skot/bitaxe/doc/bitaxe_v2.jpg

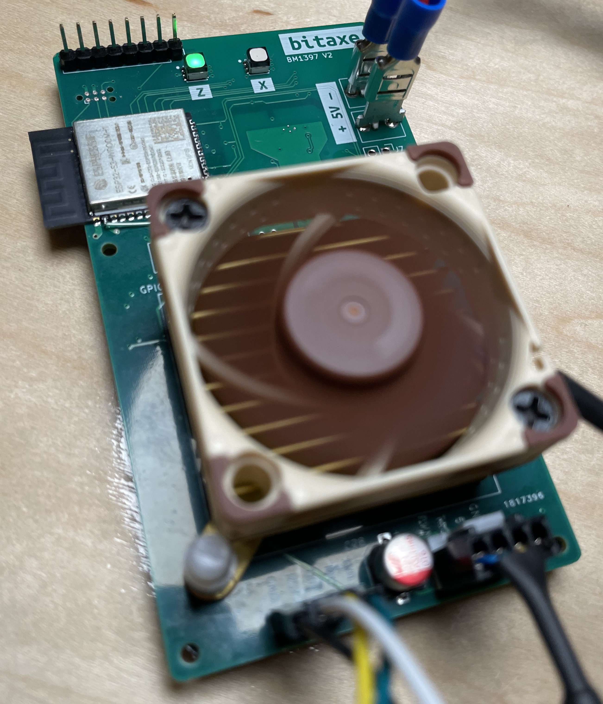
doc/bitaxe_v2.jpg
