skot/bitaxe/doc/BM1397.png

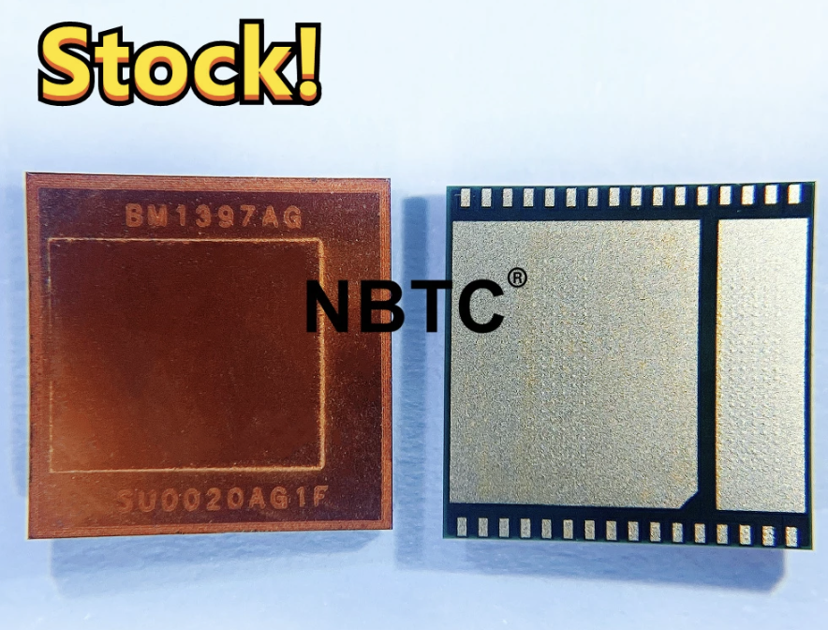
doc/BM1397.png
