skot/bitaxe/doc/fan.png

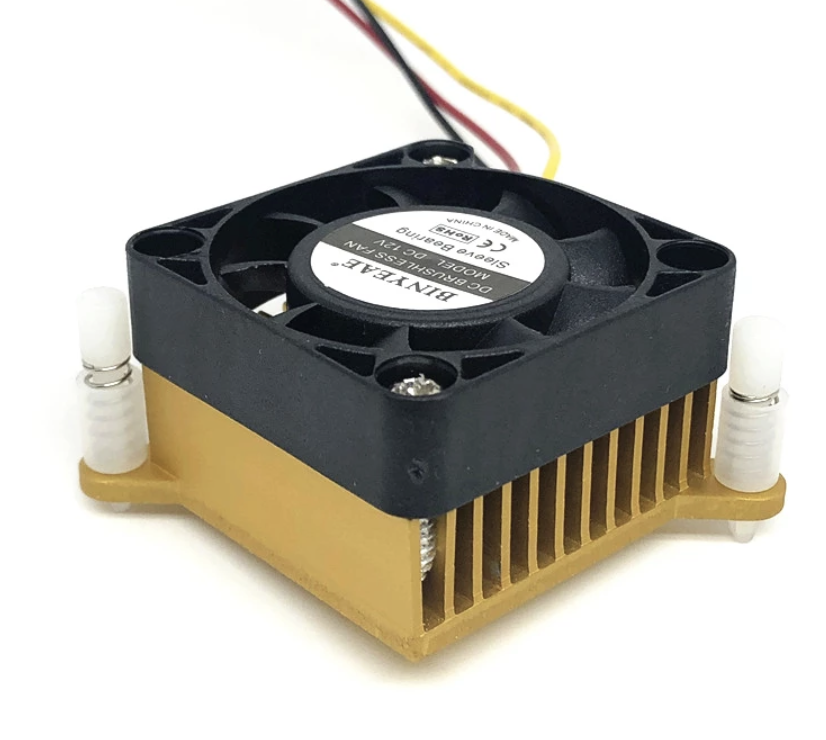
doc/fan.png
