skot/bitaxe/3d/SN74AXC1T45DBVR.STEP

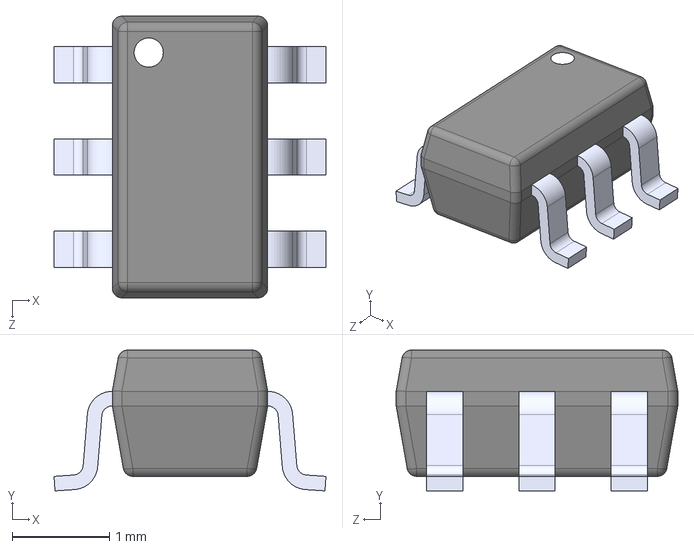
[picture p27: CAD file, 2022-11-27]
3d/SN74AXC1T45DBVR.STEP
2.80 x 1.45 x 2.90 mm
