skot/bitaxe/3d/TXB0104RGYR.STEP

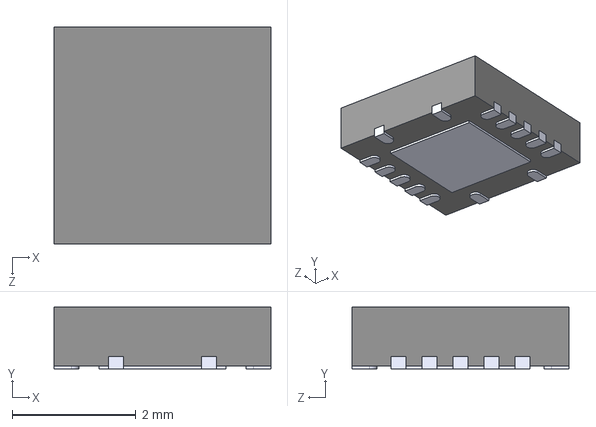
[picture p28: CAD file, 2022-11-26]
3d/TXB0104RGYR.STEP
3.50 x 1.00 x 3.50 mm
