skot/bitaxe/3d/DRC0010J.stp

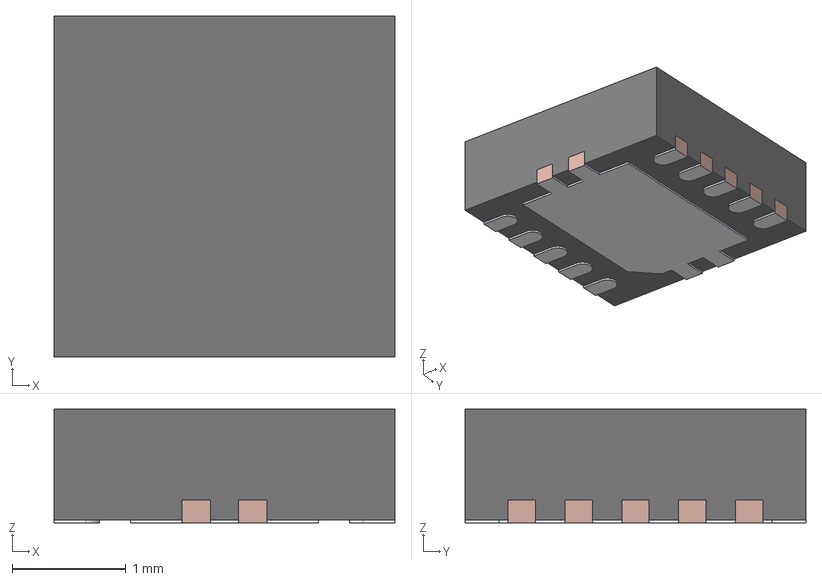
[picture p29: CAD file, 2022-11-23]
3d/DRC0010J.stp
3.00 x 3.00 x 1.00 mm
BODY-SON
FRAME-DRC0010J
