skot/bitaxe/3d/DQG0008A.stp

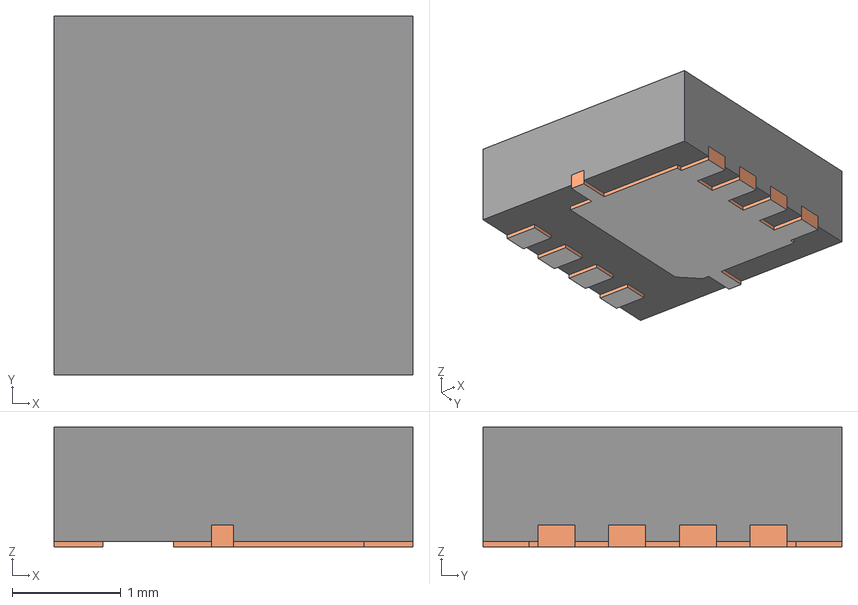
[picture p34: CAD file, 2022-11-23]
3d/DQG0008A.stp
3.30 x 3.30 x 1.10 mm
BODY-SON
FRAME-DQG0008A
PIN1-ID
