skot/bitaxe/3d/CX3225SB16000H0FLJCC.STEP

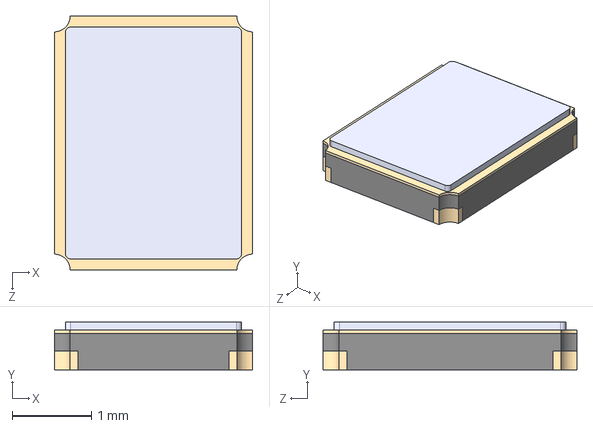
[picture p35: CAD file, 2022-10-04]
3d/CX3225SB16000H0FLJCC.STEP
2.50 x 0.6 x 3.20 mm
