skot/bitaxe/3d/DRL0006A.stp

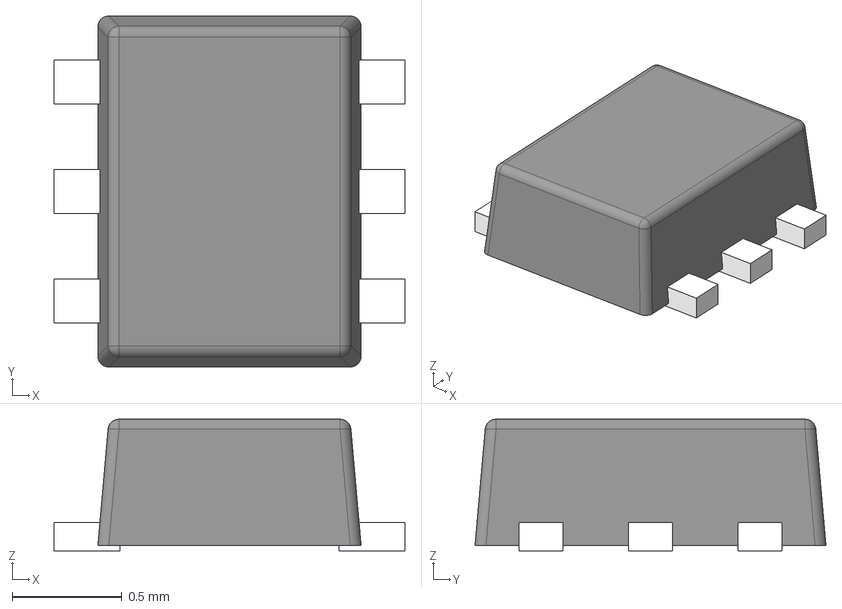
[picture p36: CAD file, 2022-06-23]
3d/DRL0006A.stp
1.60 x 1.60 x 0.6 mm
FRAME-DRL0006A
BODY-SOT
PIN1-ID
