skot/bitaxe/3d/c-63862-1-r-3d.stp

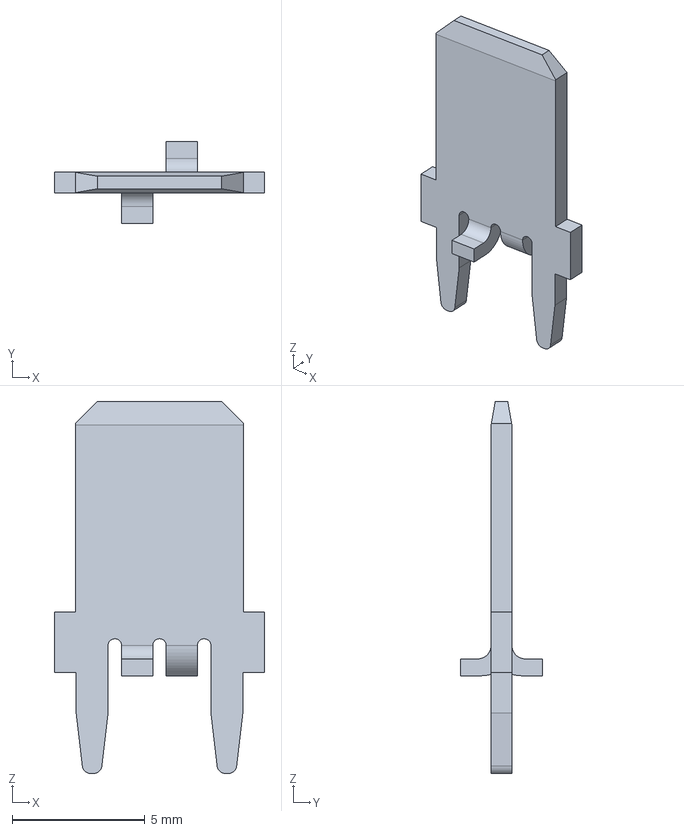
[picture p37: CAD file, 2022-06-11]
3d/c-63862-1-r-3d.stp
7.92 x 3.07 x 14.0 mm
