skot/bitaxe/3d/SMV_z90.stp

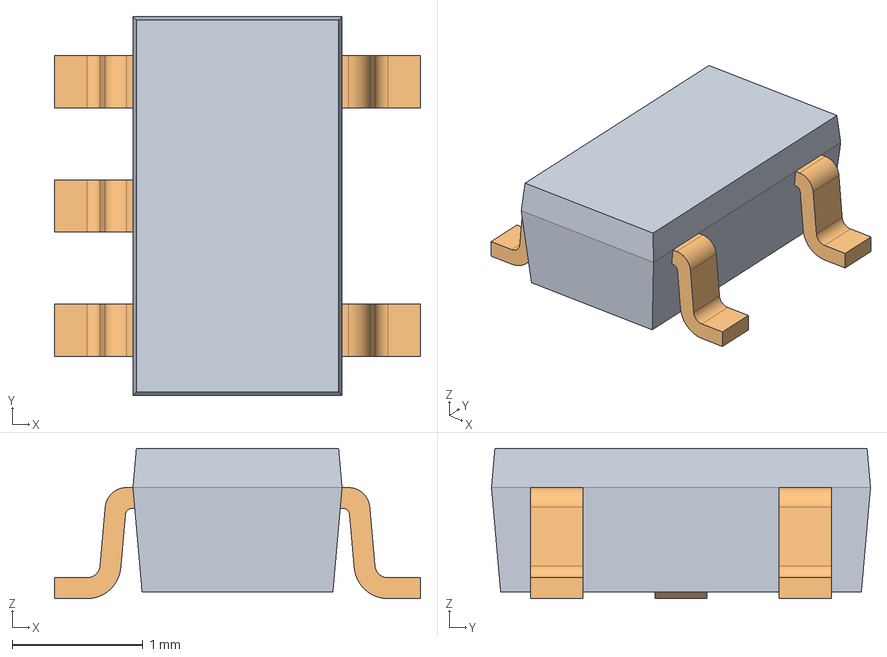
[picture p38: CAD file, 2022-06-11]
3d/SMV_z90.stp
2.80 x 2.90 x 1.15 mm
