skot/bitaxe/3d/SOT-23-5_M5_MCH.step

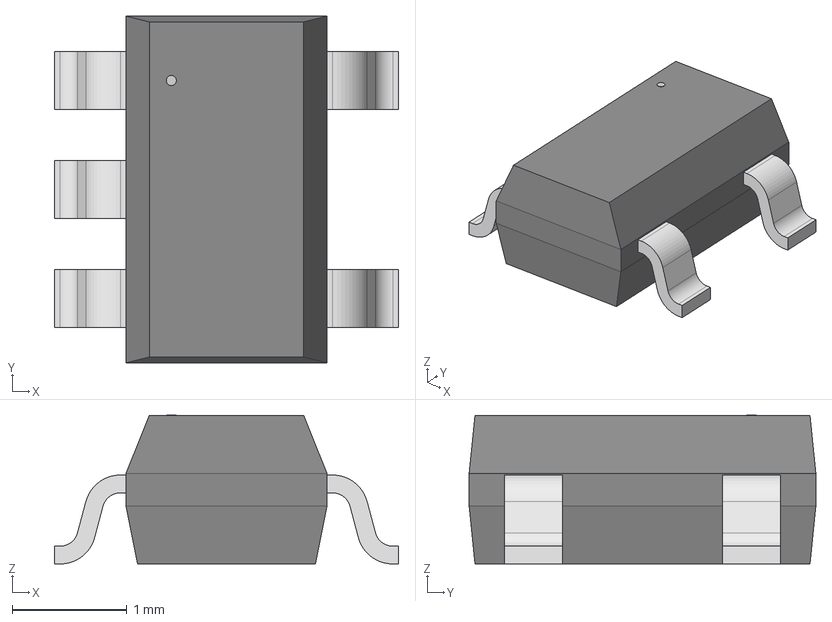
[picture p40: CAD file, 2022-03-05]
3d/SOT-23-5_M5_MCH.step
3.00 x 3.02 x 1.30 mm
