skot/bitaxe/3d/21-0164B_L622-1_MXM.step

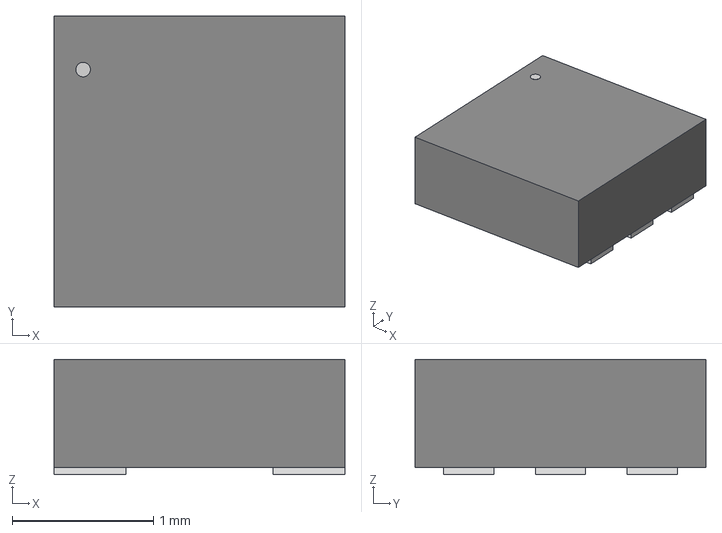
[picture p41: CAD file, 2022-03-05]
3d/21-0164B_L622-1_MXM.step
2.06 x 2.06 x 0.815 mm
