skot/bitaxe/3d/XRCGB27M120F3M10R0_MUR.step

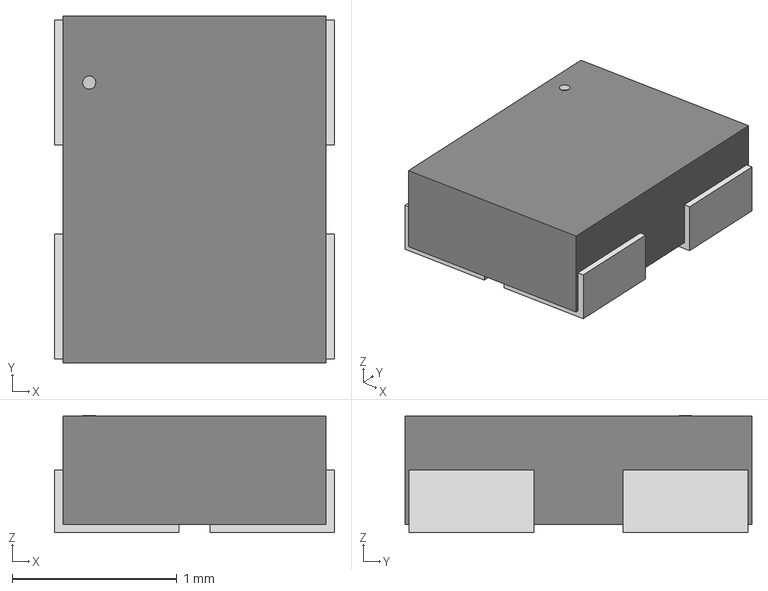
[picture p42: CAD file, 2022-03-05]
3d/XRCGB27M120F3M10R0_MUR.step
1.70 x 2.11 x 0.714 mm
